UBO-Open-factory/CTHAir-DHT22-Wifi/Production/Photos/IMG_20211122_094541.jpg

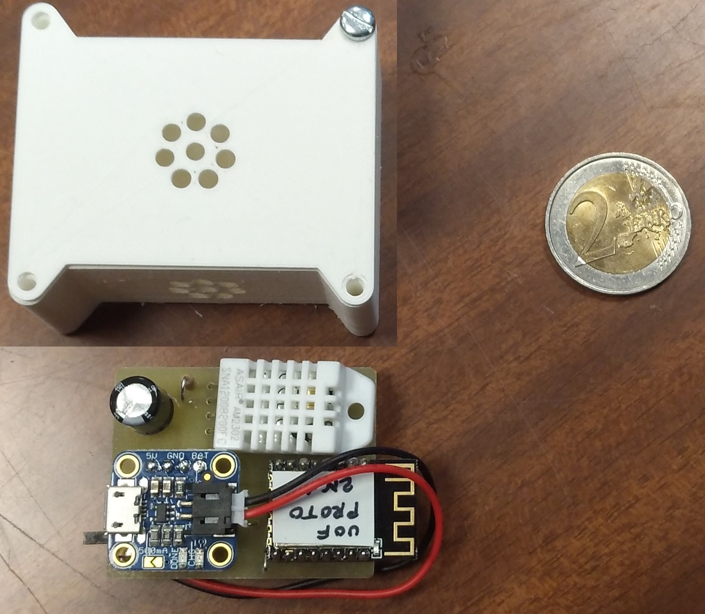
Production/Photos/IMG_20211122_094541.jpg
