UBO-Open-factory/CTHAir-DHT22-Wifi/Production/Photos/IMG_20211124_111958.jpg

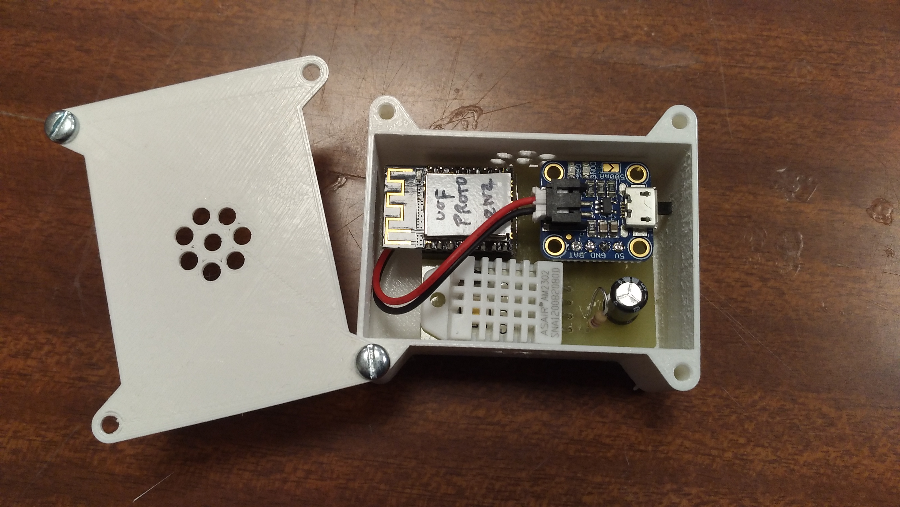
Production/Photos/IMG_20211124_111958.jpg
