UBO-Open-factory/CTHAir-DHT22-Wifi/Production/Photos/IMG_20211203_150757.jpg

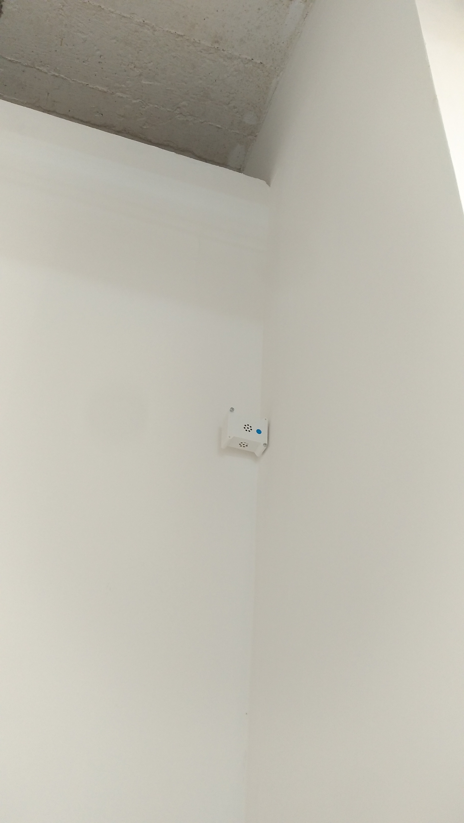
Production/Photos/IMG_20211203_150757.jpg
