UBO-Open-factory/CTHAir-DHT22-Wifi/Production/Programmateur/V1/IMG_20211203_142028.jpg

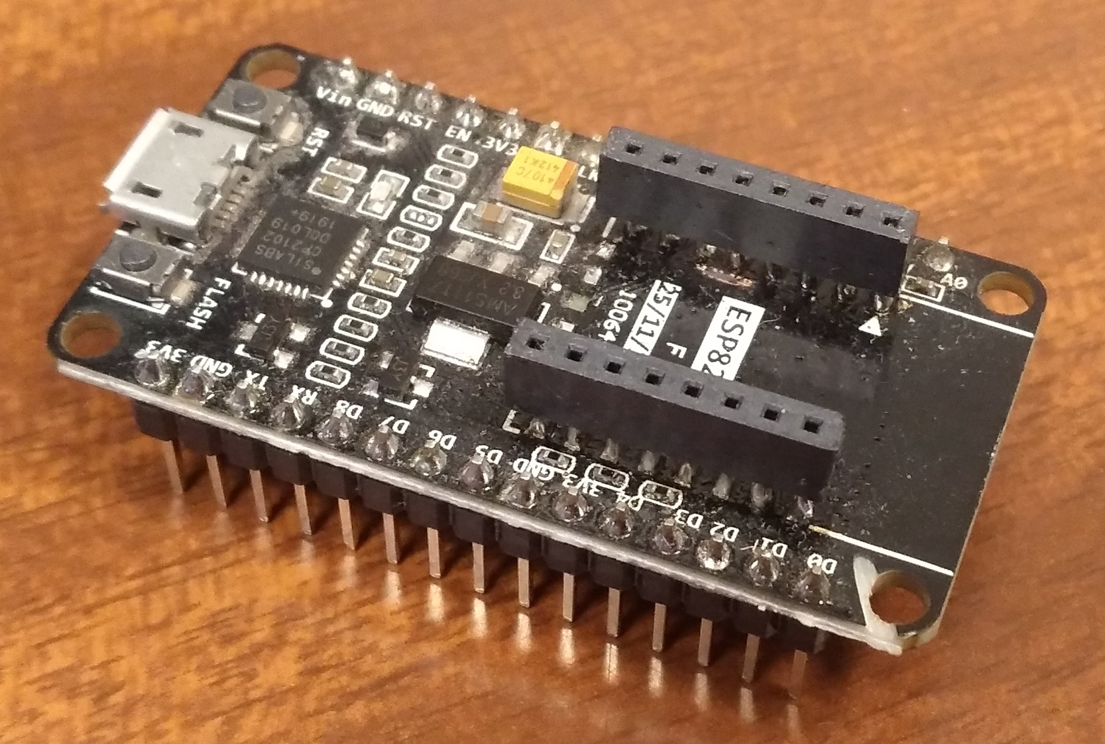
Production/Programmateur/V1/IMG_20211203_142028.jpg
