UBO-Open-factory/CTHAir-DHT22-Wifi/Production/Programmes/CTHAir_DHT22_Wifi_V2_0/wifi_data.h

//
//
//    données de connection WIFI
//
//

// nom du réseau Wifi auquel on veut connecter le module
const char* ssid = "xxxxx";

// mot de passe du réseau wifi auquel on veut connecter le module
const char* password = "xxxxx";
